michaeljbraus/iplate-suite/wid-files-soil-bacteria/bacterial-isolation-device-v1.1-screenshot.png

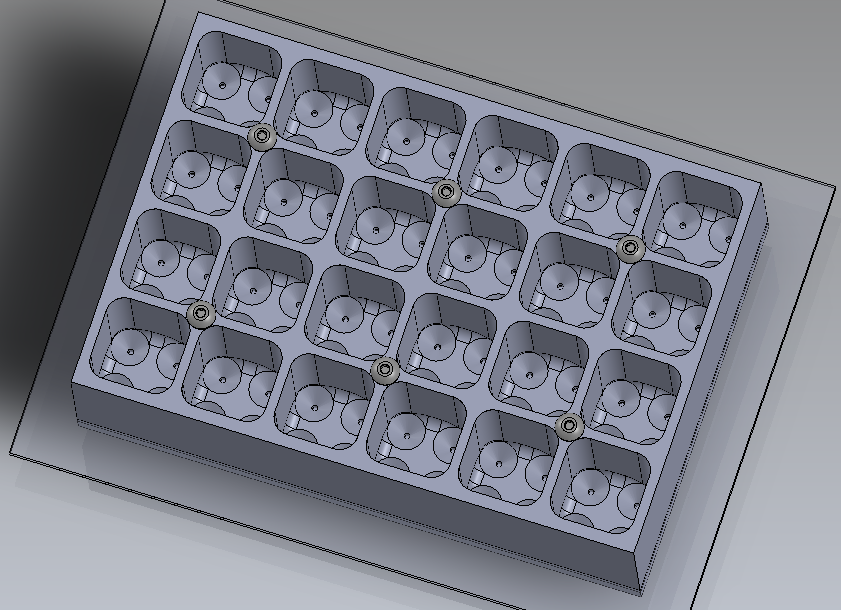
wid-files-soil-bacteria/bacterial-isolation-device-v1.1-screenshot.png
